NPPC-UK/Gravimetrics/Database/ERD/gravi_ERD.png

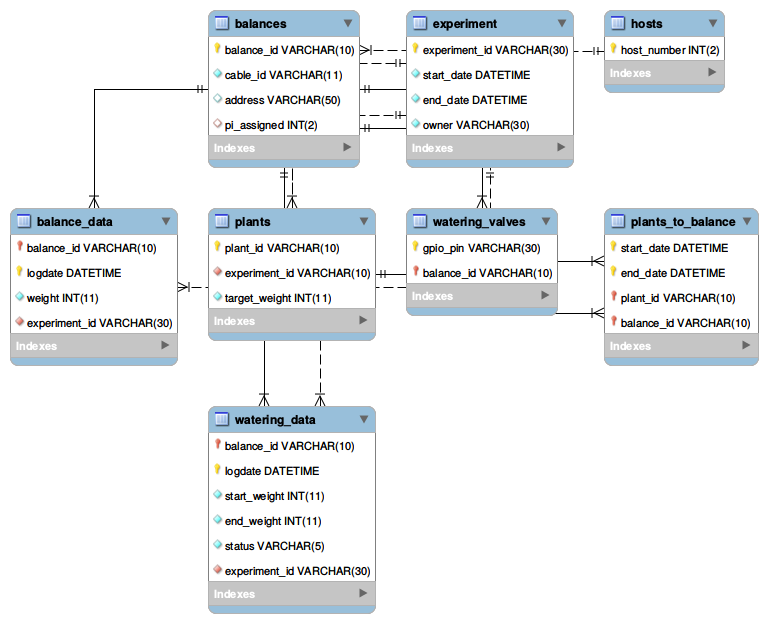
Database/ERD/gravi_ERD.png
