NPPC-UK/Gravimetrics/Documents/Diagrams/Lifter/lifter_sketch.jpg

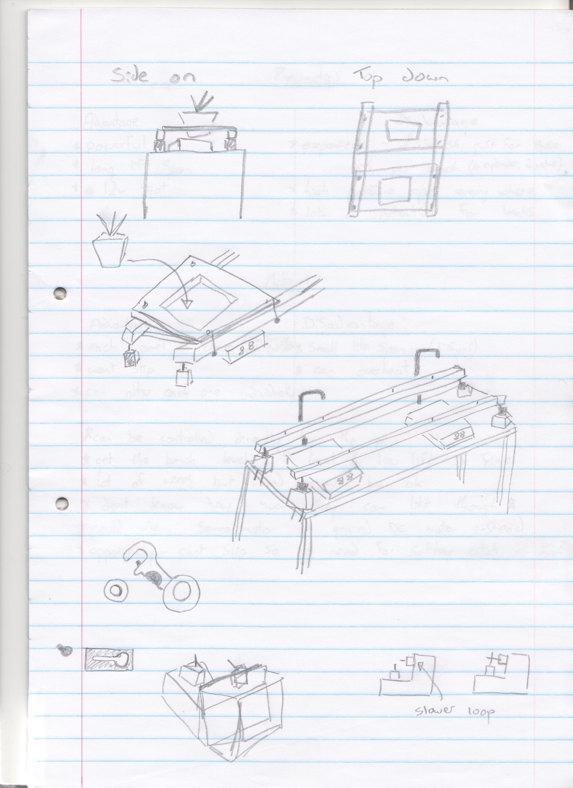
Documents/Diagrams/Lifter/lifter_sketch.jpg
